KytorIndustries/SCARTpoint/photos/Kit_SCARTpoint_Lower_Input.jpg

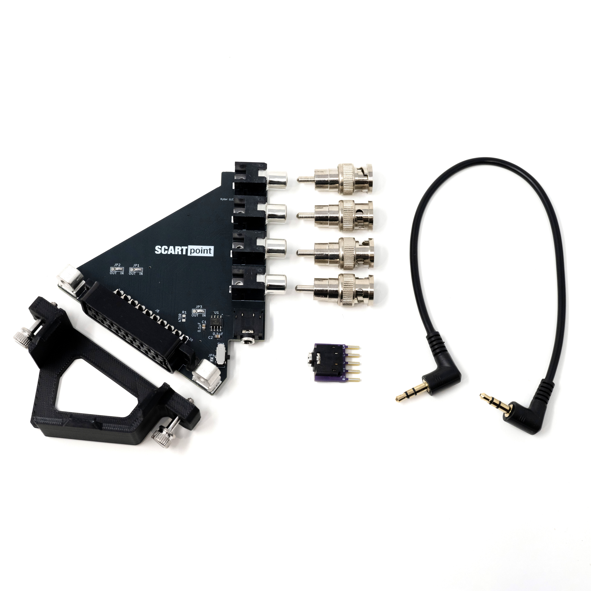
photos/Kit_SCARTpoint_Lower_Input.jpg
