KytorIndustries/SCARTpoint/photos/Kit_SCARTpoint_Upper_Output.jpg

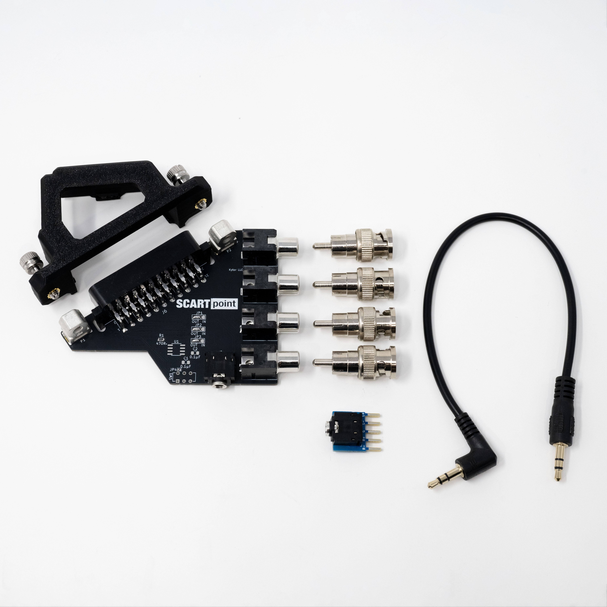
photos/Kit_SCARTpoint_Upper_Output.jpg
