KytorIndustries/SCARTpoint/photos/Renders/SCARTpoint-lower2.png

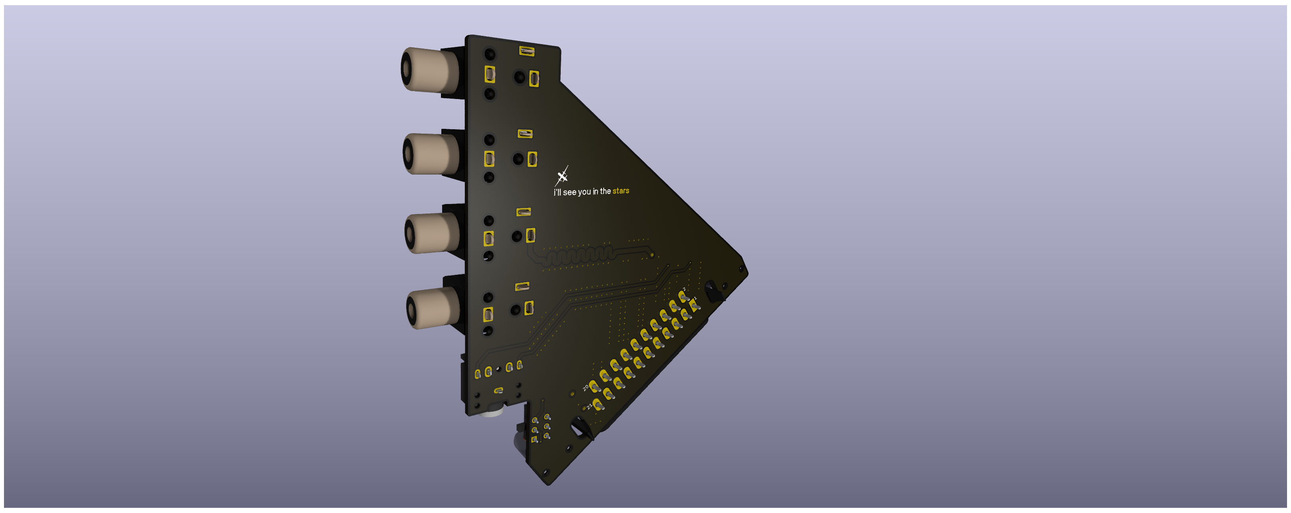
photos/Renders/SCARTpoint-lower2.png
