KytorIndustries/SCARTpoint/photos/Renders/SCARTpoint-upper2.png

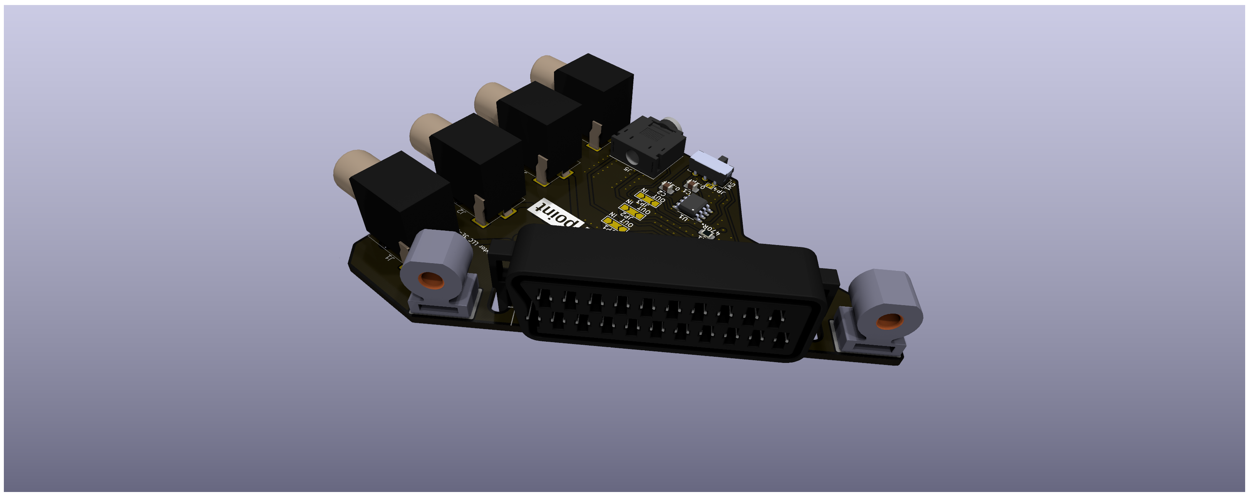
photos/Renders/SCARTpoint-upper2.png
