KytorIndustries/SCARTpoint/photos/Renders/SCARTpoint-upper3.png

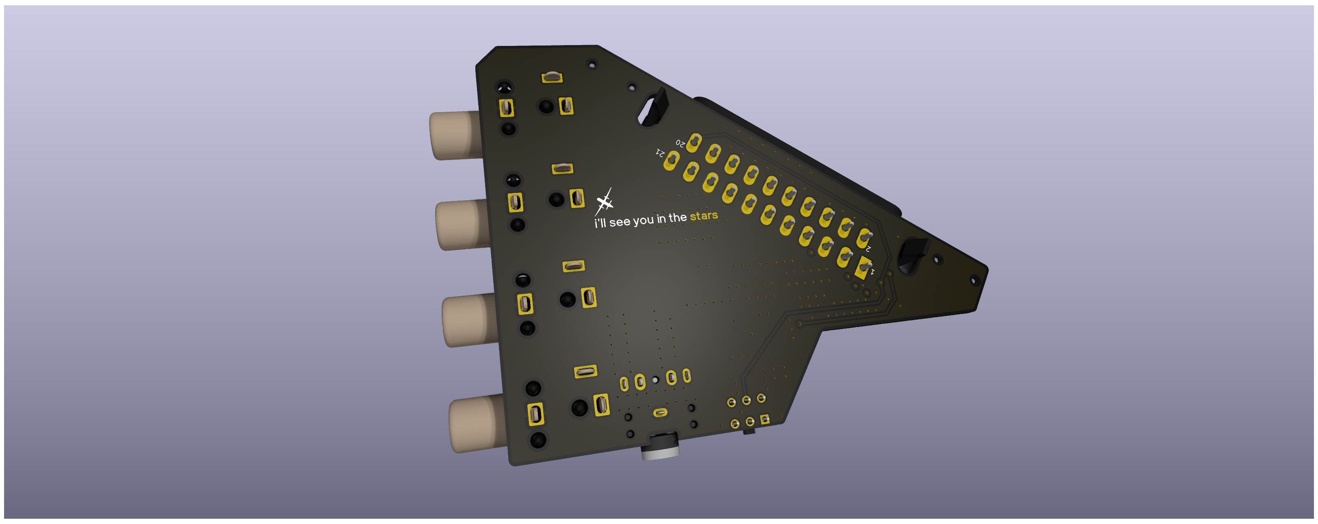
photos/Renders/SCARTpoint-upper3.png
