KytorIndustries/SCARTpoint/photos/SCARTpoint_Lower_Input_Top.jpg

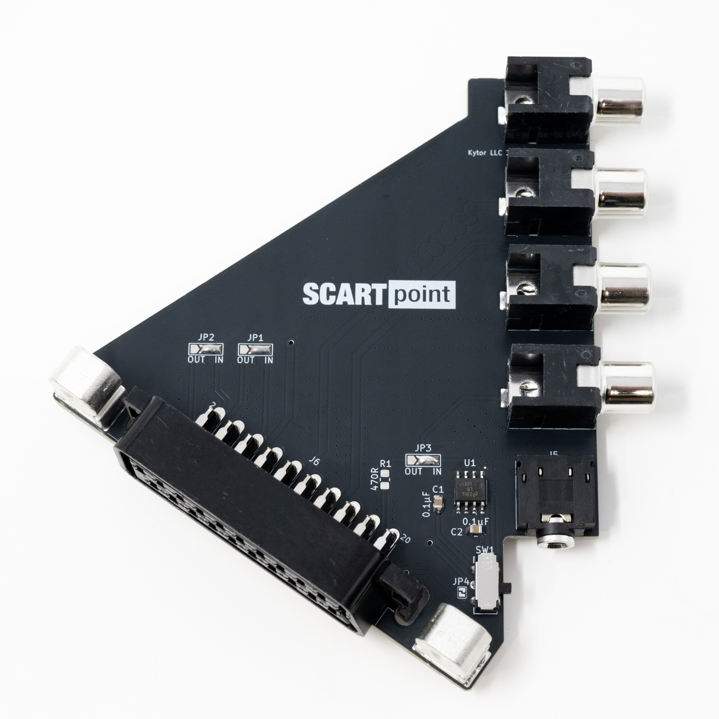
photos/SCARTpoint_Lower_Input_Top.jpg
