KytorIndustries/SCARTpoint/photos/SCARTpoint_Lower_Output_Bottom.jpg

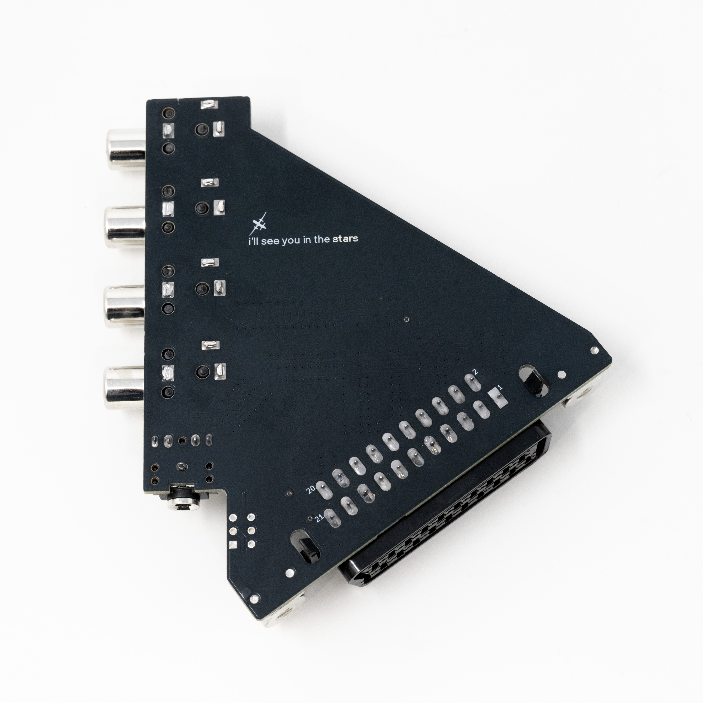
photos/SCARTpoint_Lower_Output_Bottom.jpg
