KytorIndustries/SCARTpoint/photos/SCARTpoint_Lower_Output_Top.jpg

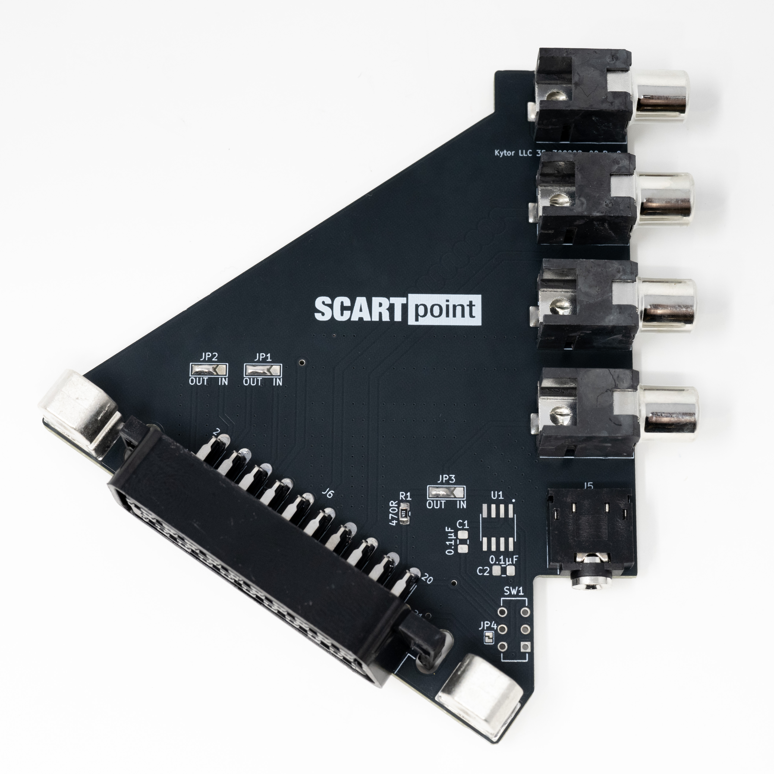
photos/SCARTpoint_Lower_Output_Top.jpg
