KytorIndustries/SCARTpoint/photos/SCARTpoint_Upper_Input.jpg

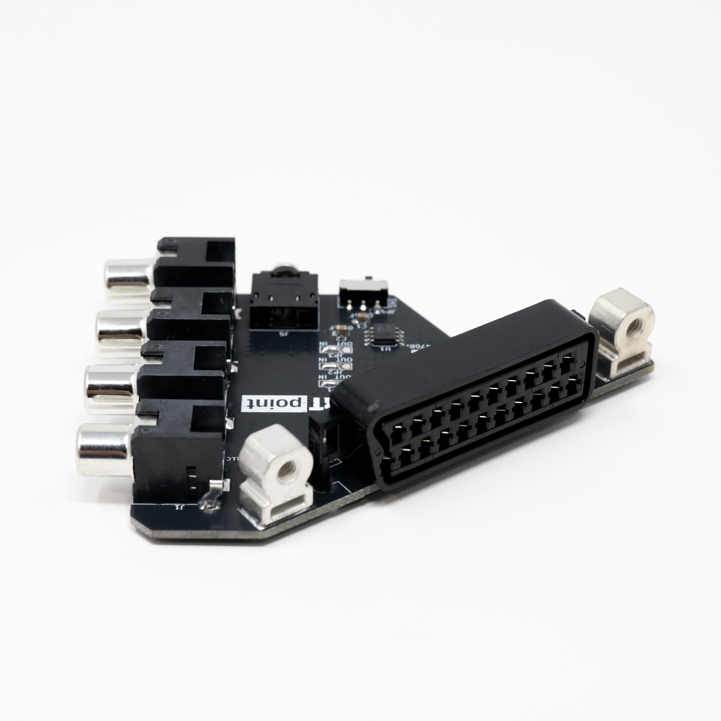
photos/SCARTpoint_Upper_Input.jpg
