KytorIndustries/SCARTpoint/photos/SCARTpoint_Upper_Input_Bottom.jpg

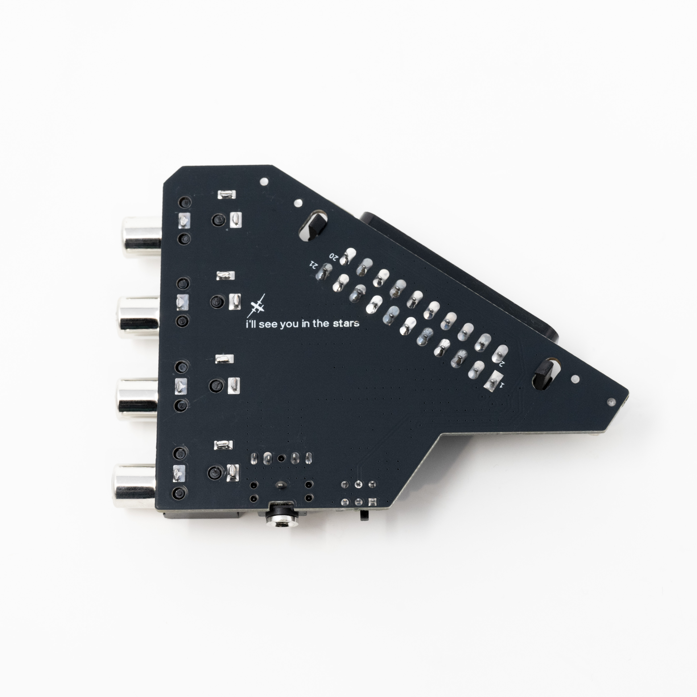
photos/SCARTpoint_Upper_Input_Bottom.jpg
