KytorIndustries/SCARTpoint/photos/SCARTpoint_Upper_Input_Top.jpg

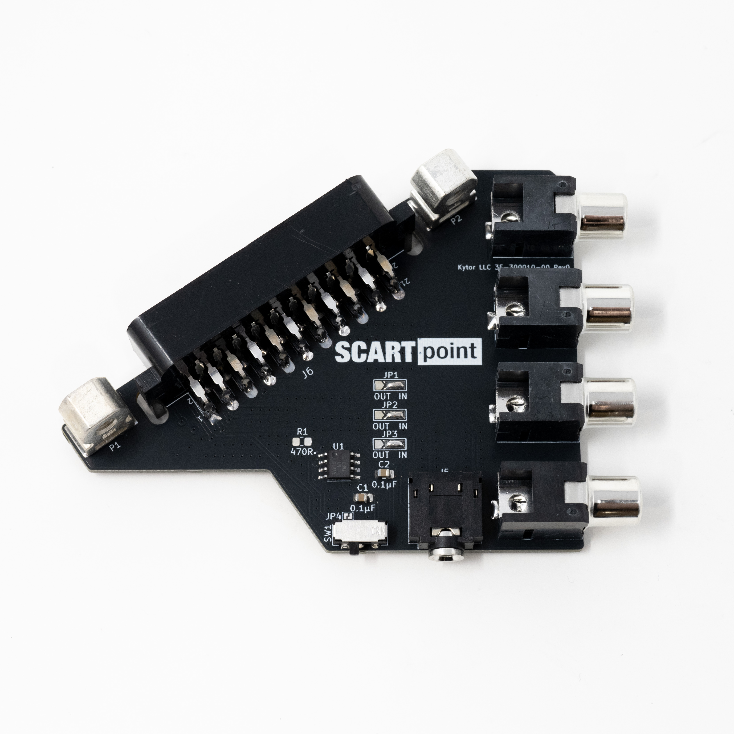
photos/SCARTpoint_Upper_Input_Top.jpg
