KytorIndustries/SCARTpoint/photos/SCARTpoint_Upper_Output_Top.jpg

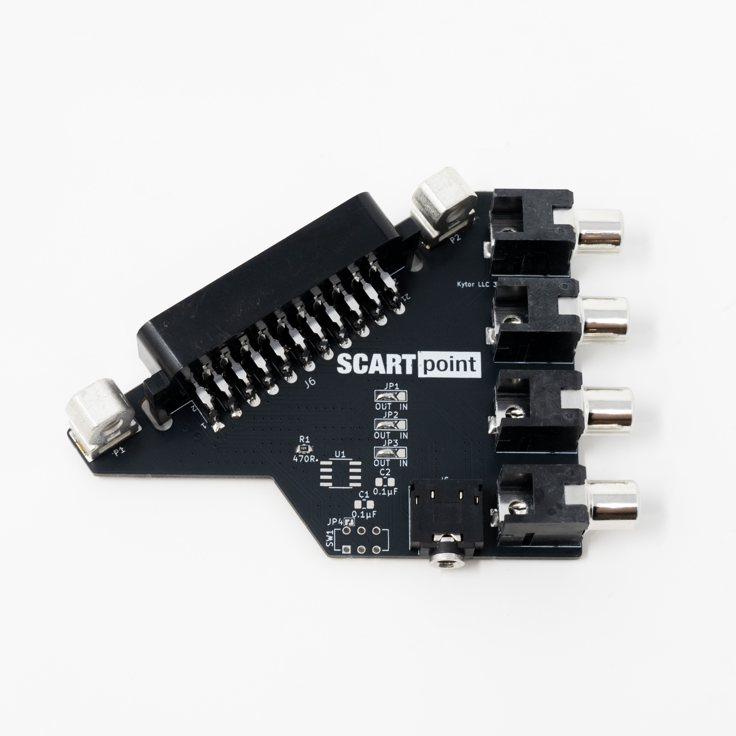
photos/SCARTpoint_Upper_Output_Top.jpg
